Mark-MDO47/KnowHow_ParkTheCar/images/box_HC-SR04.png

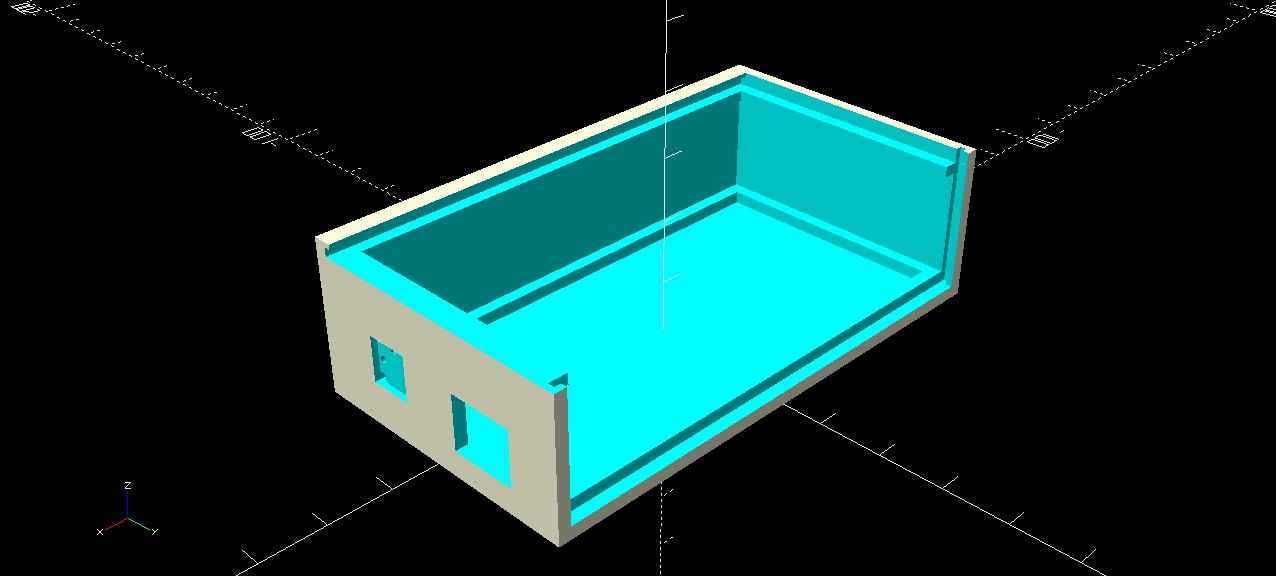
images/box_HC-SR04.png
