Mark-MDO47/KnowHow_ParkTheCar/images/IMG07751.JPG

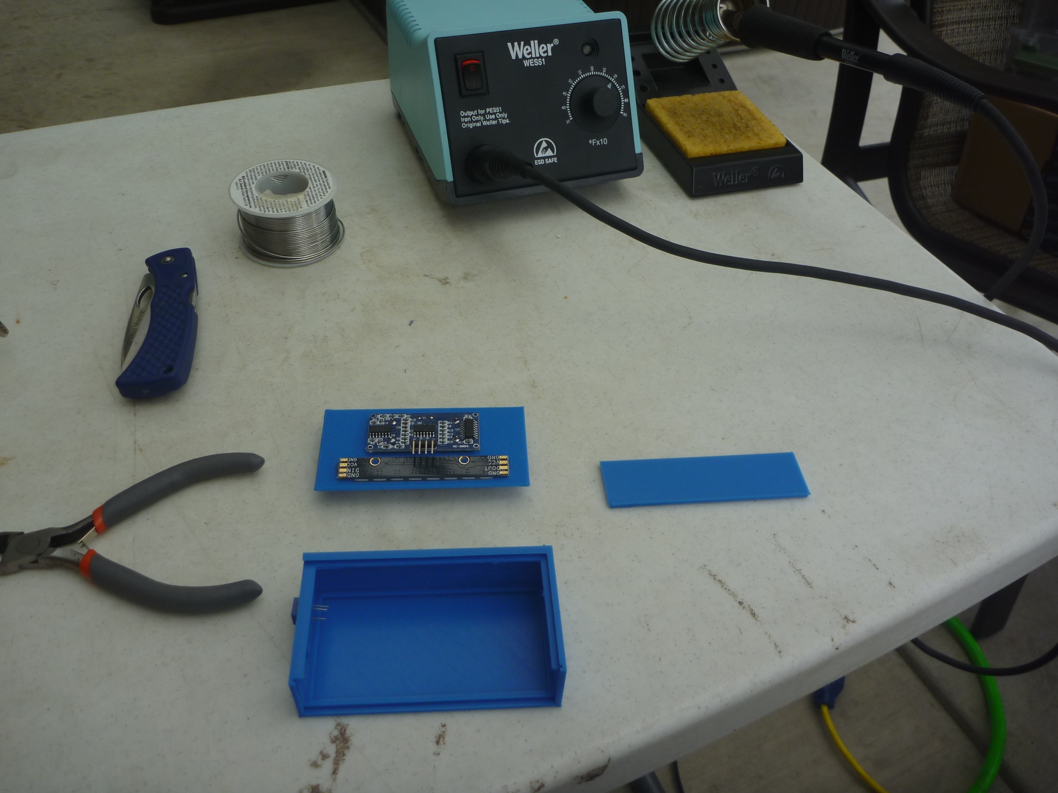
images/IMG07751.JPG
