Mark-MDO47/KnowHow_ParkTheCar/images/IMG07753.JPG

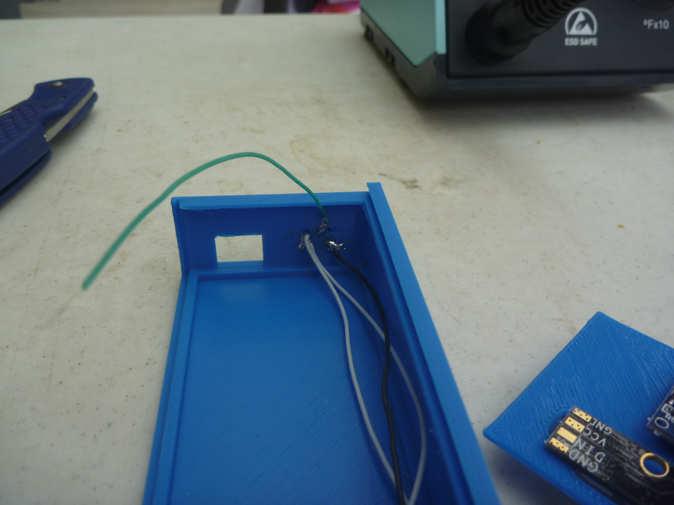
images/IMG07753.JPG
