Mark-MDO47/KnowHow_ParkTheCar/images/IMG07754.JPG

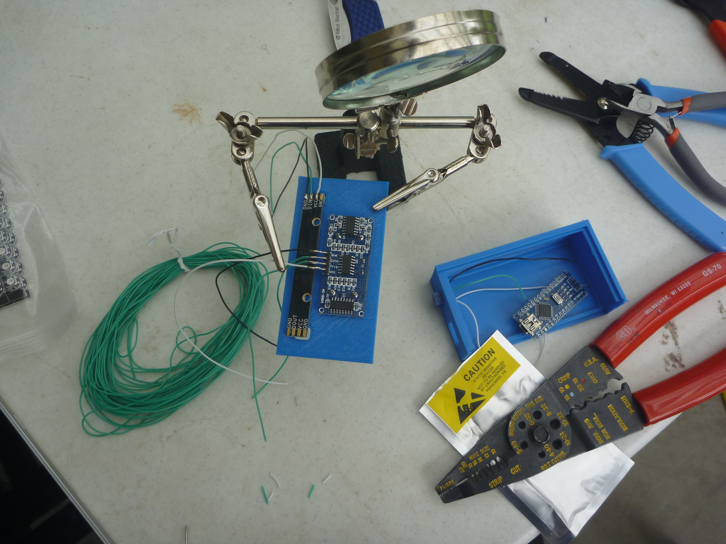
images/IMG07754.JPG
