Mark-MDO47/KnowHow_ParkTheCar/images/IMG07755.JPG

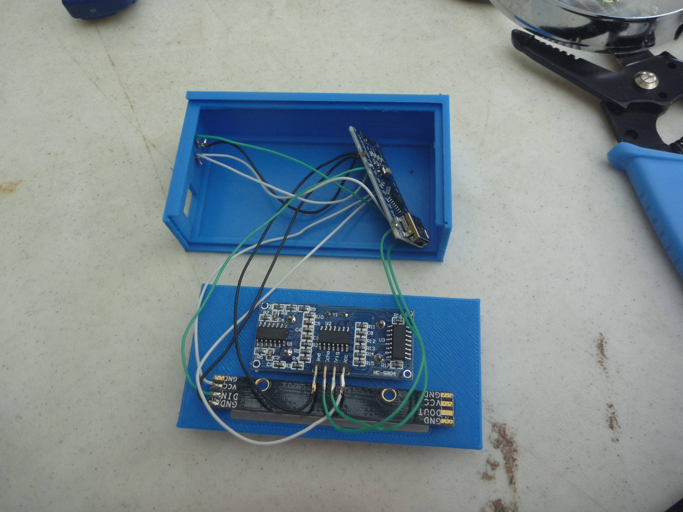
images/IMG07755.JPG
