Mark-MDO47/KnowHow_ParkTheCar/images/IMG07757.JPG

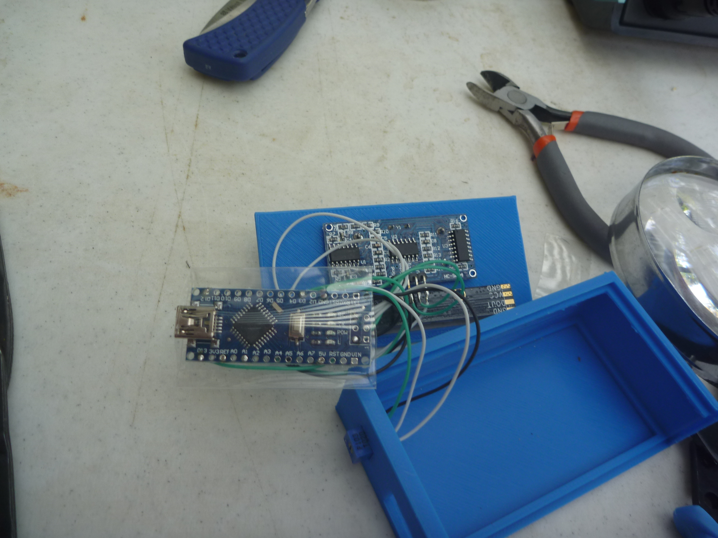
images/IMG07757.JPG
