Mark-MDO47/KnowHow_ParkTheCar/images/IMG07759.JPG

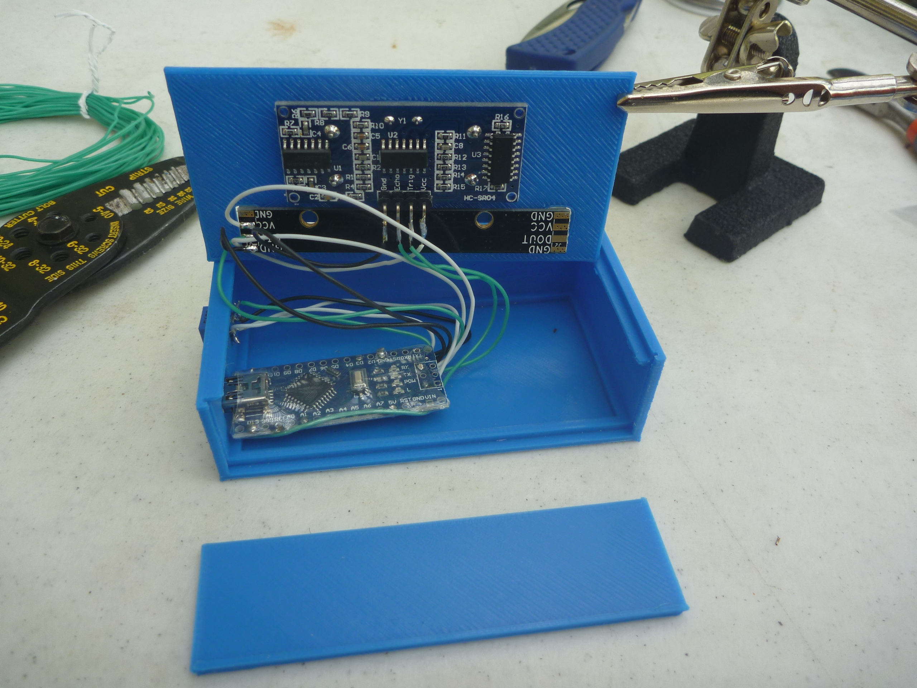
images/IMG07759.JPG
