Mark-MDO47/KnowHow_ParkTheCar/images/IMG07760.JPG

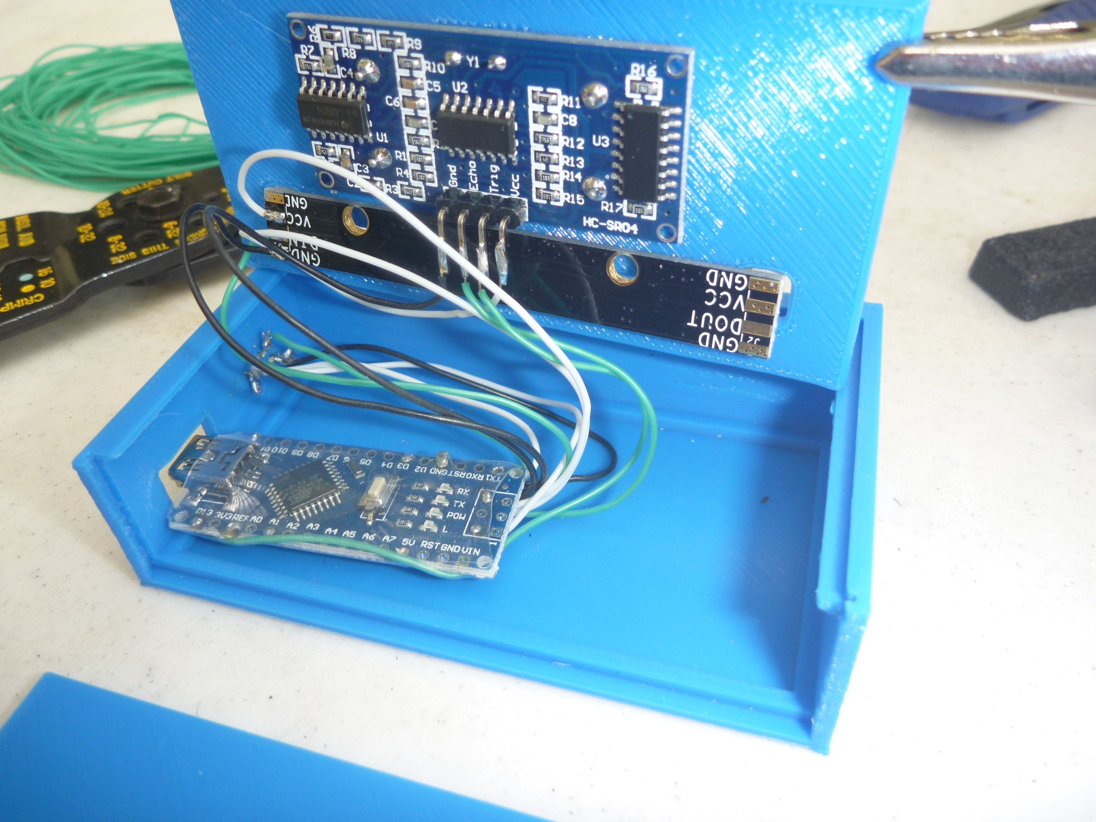
images/IMG07760.JPG
