Mark-MDO47/KnowHow_ParkTheCar/images/IMG07764.JPG

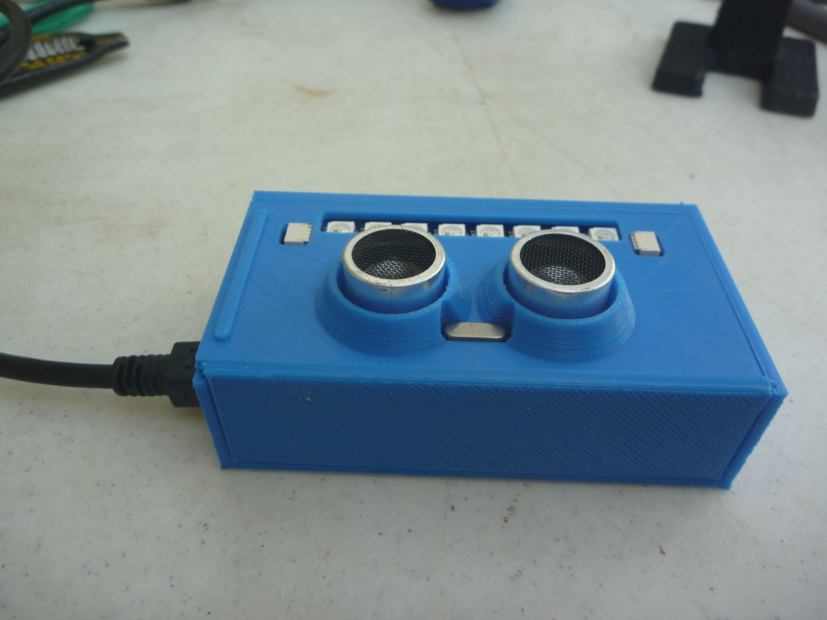
images/IMG07764.JPG
