Mark-MDO47/KnowHow_ParkTheCar/images/IMG07765.JPG

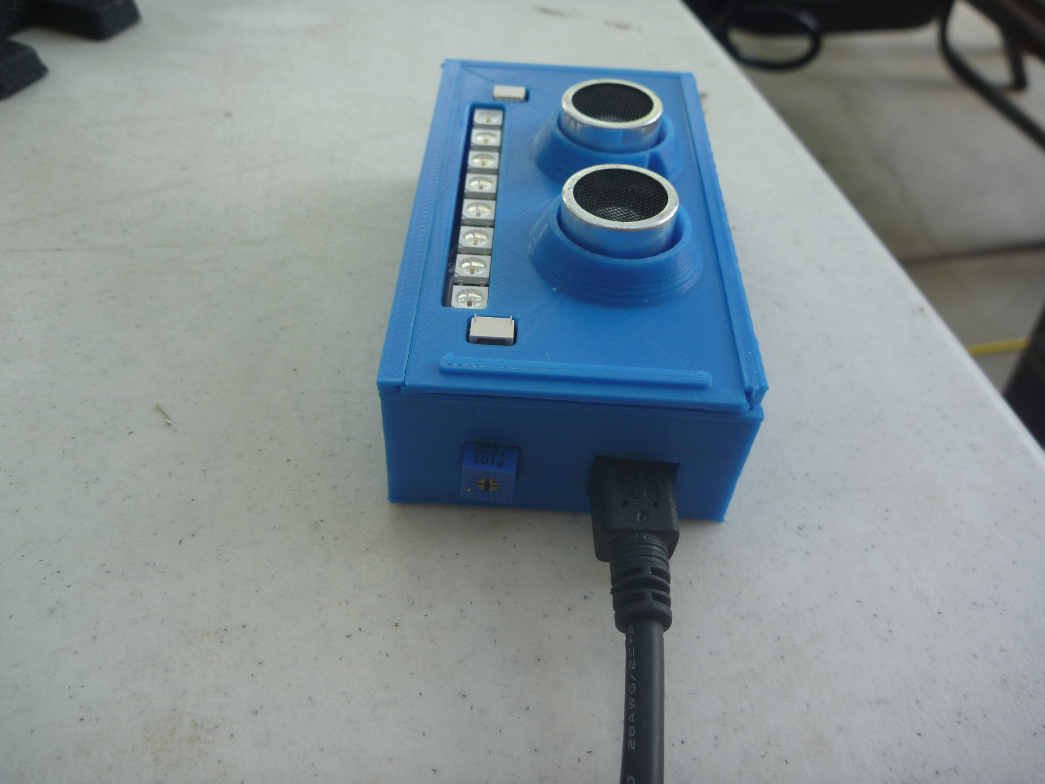
images/IMG07765.JPG
